ranji0599/Master-Thesis/MTP_Docs/Prototype Photos/1st Version of Circuit along with 1st version of Electrode.jpg

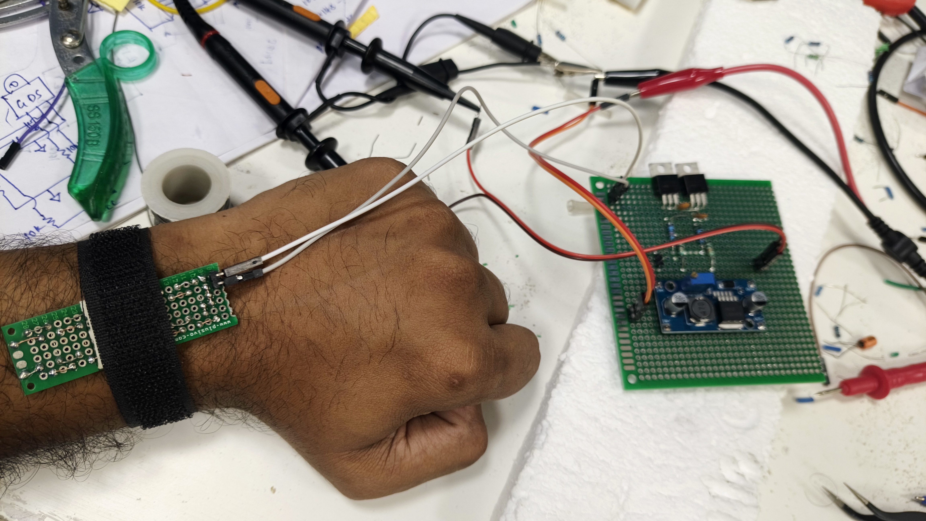
MTP_Docs/Prototype Photos/1st Version of Circuit along with 1st version of Electrode.jpg
