ranji0599/Master-Thesis/MTP_Docs/Prototype Photos/Electrode Chemical Etching Process.jpg

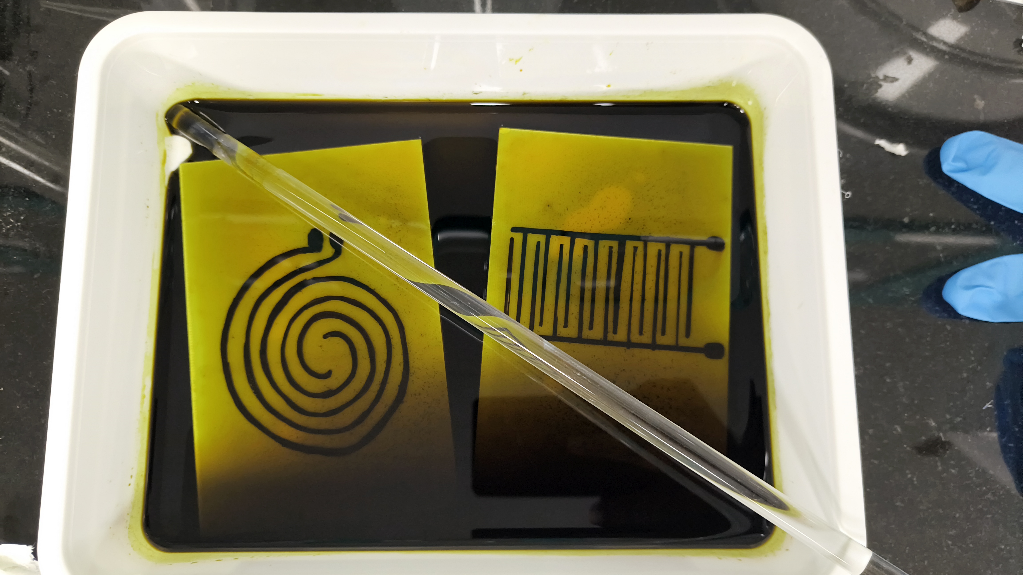
MTP_Docs/Prototype Photos/Electrode Chemical Etching Process.jpg
