ranji0599/Master-Thesis/MTP_Docs/Prototype Photos/IMG_20260527_194227_716.jpg

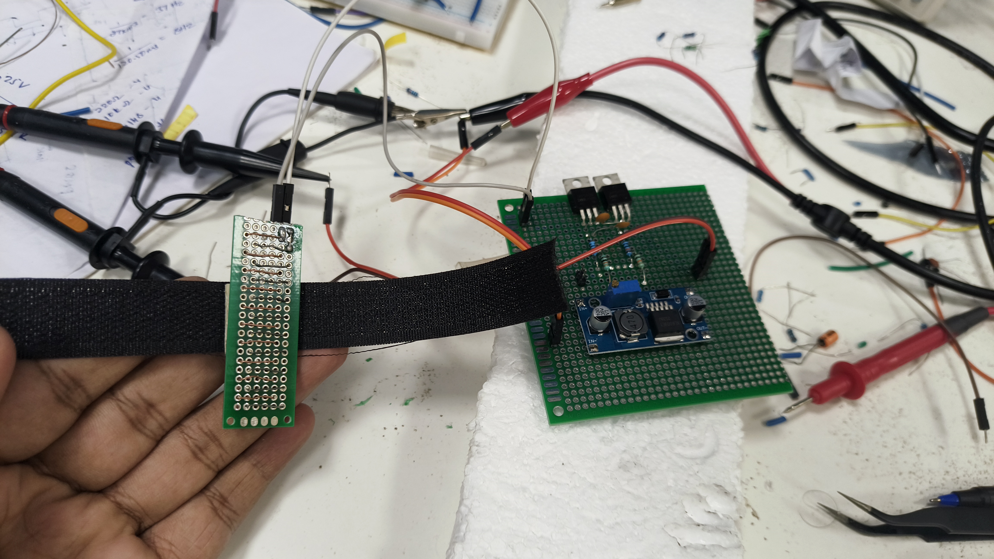
MTP_Docs/Prototype Photos/IMG_20260527_194227_716.jpg
