ranji0599/Master-Thesis/MTP_Docs/Prototype Photos/Versions of Electrode Fabricated through Chemical Etching.jpg

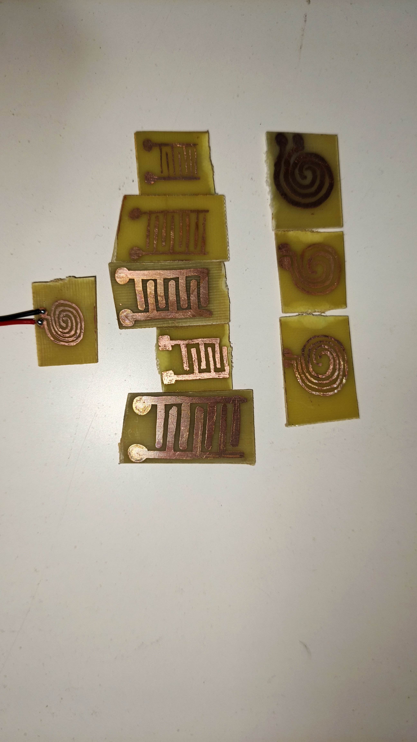
MTP_Docs/Prototype Photos/Versions of Electrode Fabricated through Chemical Etching.jpg
