ranji0599/Master-Thesis/MTP_Docs/Prototype Photos/Final Electrode Considered for Testing.jpg

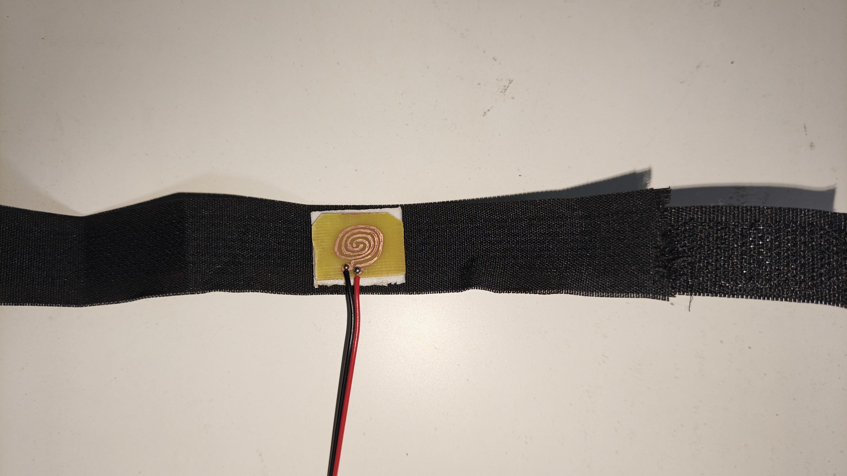
MTP_Docs/Prototype Photos/Final Electrode Considered for Testing.jpg
